tonykoop/marimba/validation-loop.csv

check_id | packet_artifact | readiness_before | prediction_source | target | tolerance | method | measured_result | status | next_action | evidence | source_status
vl001 | family-spec.csv | L1_packet | workbook free-free beam model; marimba-design-table.xlsx | C3/A4/C6 pilot bars hit target pitch after arching and sanding | measurement_required; record cents error at each stage | Strike bars on soft supports at node_1/node_2, log tuner Hz at flat_blank/post_arch/post_sand/final_frame | TBD | measurement_required | Build and measure C3, A4, and C6 pilots before releasing the full 37-bar cut sequence. | validation.csv has empty measured_hz and cents_error fields | workbook_model_unvalidated
vl002 | cad/design-table-inputs.csv | L1_packet | family-spec.csv and workbook-derived configuration rows | Each CAD/configuration row matches the intended note schedule and node positions | +/- 0.020 in for node placement after drawing/CAM review | Spot-check C3/A4/C6 dimensions against CAD exports, then script-check all rows before CAM | TBD | measurement_required | Compare DXF/CAD exports against family-spec.csv before cutting production blanks. | cad/design-table-inputs.csv | needs_cad_review
vl003 | drawings/marimba-pilot-plate.dxf | L1_packet | family-spec.csv pilot rows | Pilot DXF represents C3/A4/C6 outlines and node positions only | air-cut and ruler/caliper verification required | Open in CAD/CAM, verify units are inches, then air-cut or print-check the pilot plate | TBD | measurement_required | Use pilot DXF for layout review only until CAM post and shop setup are selected. | visual-output-register.csv DXF-001 | pilot_only
vl004 | family-spec.csv | L1_packet | quarter-wave resonator estimate with bore proxy from bar width | Resonators reinforce target bars without buzz or unwanted pitch shift | measurement_required after tube ID/material selection | Select actual tube ID/material, recalculate length, then test coupled response under C3/A4/C6 | TBD | measurement_required | Replace width-based bore proxy with sourced tube ID before final resonator cuts. | README Status notes tube bore TBD | supplier_spec_unverified
vl005 | bom.csv | L1_packet | workbook material assumption and sourcing placeholders | Padauk or substitute stock has known density, moisture, and defect limits | measurement_required before full blank preparation | Record board species, density estimate, moisture content, grain orientation, and defects | TBD | measurement_required | Verify current material source and log board measurements before machining. | sourcing.csv | needs_current_check
vl006 | cnc/operations.csv | L1_packet | pre-CAM CNC operation graph | Fixture, tab, arch, and drill operations preserve datums through both sides | air-cut plus pilot build required | Run fixture dry-fit and air-cut with the C3/A4/C6 pilot sequence before full set | TBD | measurement_required | Keep OP-205 and OP-900 as blockers until pilot data exists. | cnc/operations.csv | pre_cam
vl007 | cad/mcp-session-log.md | L1_packet | V5 provenance contract | Any MCP-derived CAD/render/Adobe/image artifact has a logged session row | required before claiming V5 build-packet candidate | Append session_id, tool, parent_artifact, and artifact path during each future MCP run | TBD | blocked | Do not claim V5 candidate until provenance exists for new V5 deliverables. | cad/mcp-session-log.md | no_mcp_sessions_logged
