tonykoop/marimba/docs/marimba-piano/tuning-targets-c4-c5.csv

note | midi | f_hz | padauk_flat_0p75in_bar_est_len_in | hard_maple_flat_0p75in_bar_est_len_in | aluminum_6061_flat_0p375in_bar_est_len_in | res_tube_1p5in_id_est_len_in | res_tube_2p0in_id_est_len_in | status | notes
C4 | 60 | 261.63 | 21.11 | 22.14 | 17.12 | 11.72 | 11.31 | derived_estimate | Free-free flat-bar and quarter-wave estimates; not cut-ready.
C#4 | 61 | 277.18 | 20.51 | 21.51 | 16.64 | 10.99 | 10.58 | derived_estimate | Free-free flat-bar and quarter-wave estimates; not cut-ready.
D4 | 62 | 293.66 | 19.92 | 20.90 | 16.16 | 10.31 | 9.90 | derived_estimate | Free-free flat-bar and quarter-wave estimates; not cut-ready.
D#4 | 63 | 311.13 | 19.36 | 20.30 | 15.70 | 9.66 | 9.25 | derived_estimate | Free-free flat-bar and quarter-wave estimates; not cut-ready.
E4 | 64 | 329.63 | 18.81 | 19.73 | 15.26 | 9.05 | 8.64 | derived_estimate | Free-free flat-bar and quarter-wave estimates; not cut-ready.
F4 | 65 | 349.23 | 18.27 | 19.16 | 14.82 | 8.47 | 8.06 | derived_estimate | Free-free flat-bar and quarter-wave estimates; not cut-ready.
F#4 | 66 | 369.99 | 17.75 | 18.62 | 14.40 | 7.93 | 7.52 | derived_estimate | Free-free flat-bar and quarter-wave estimates; not cut-ready.
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
